EngThi/Edge-Nexus/Docs/assets/cartNVIDIA.png

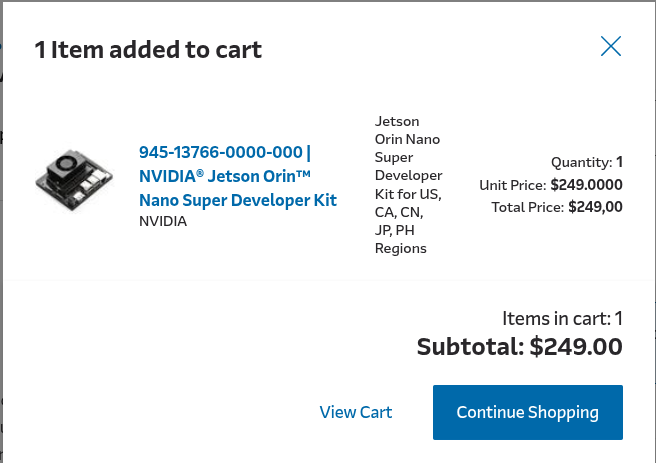
Docs/assets/cartNVIDIA.png
