EngThi/Edge-Nexus/Docs/assets/full_case_render.png

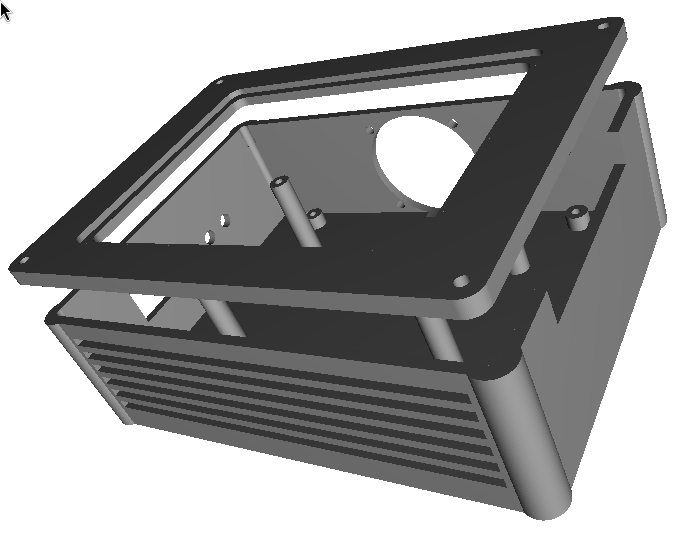
Docs/assets/full_case_render.png
