EngThi/Edge-Nexus/Docs/assets/jlcpcb_shipping_options.png

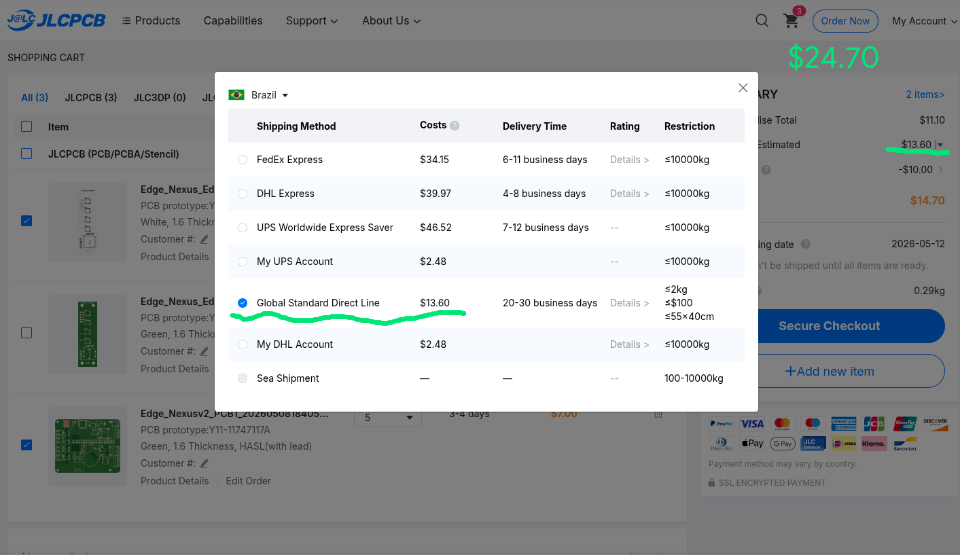
Docs/assets/jlcpcb_shipping_options.png
