EngThi/Edge-Nexus/Docs/assets/placa3D.png

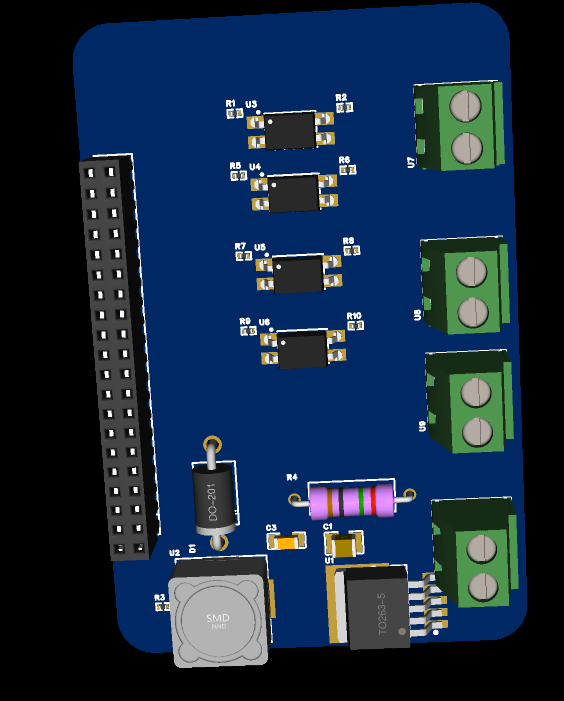
Docs/assets/placa3D.png
